Tactile-electronics/WearableTechBadgeWorkshop/images/555flashersmall.gif

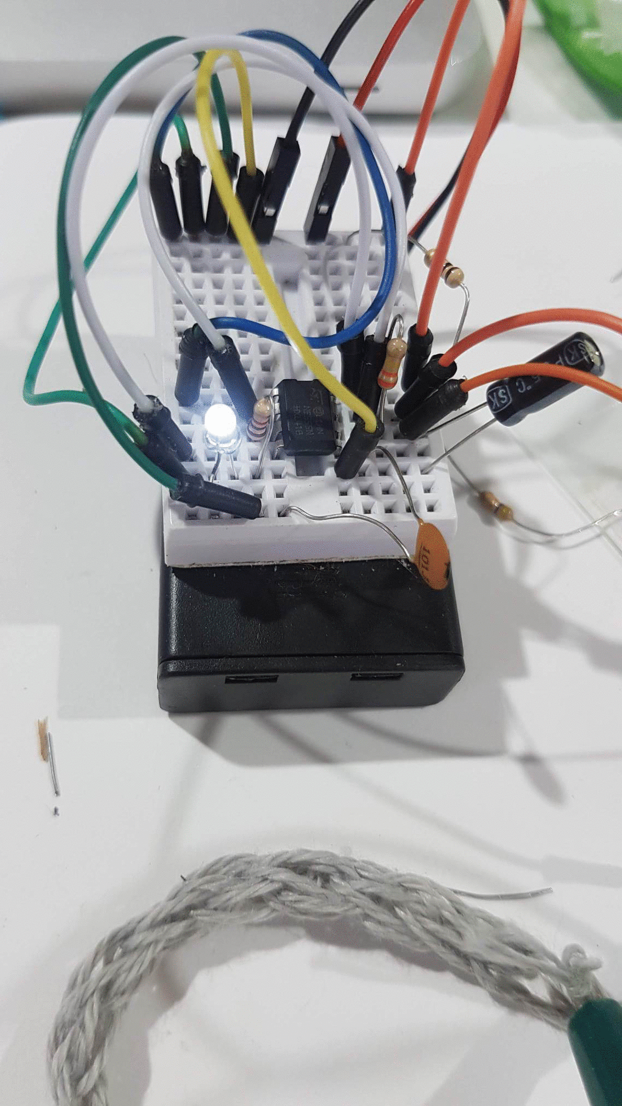
images/555flashersmall.gif
