Tactile-electronics/WearableTechBadgeWorkshop/images/session1/1/basic-sensor-circuit-1.jpg

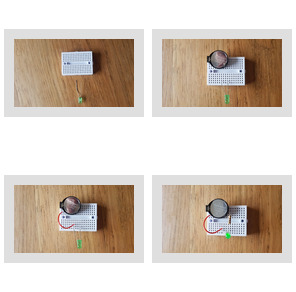
images/session1/1/basic-sensor-circuit-1.jpg
