Tactile-electronics/WearableTechBadgeWorkshop/images/session1/2/6.jpg

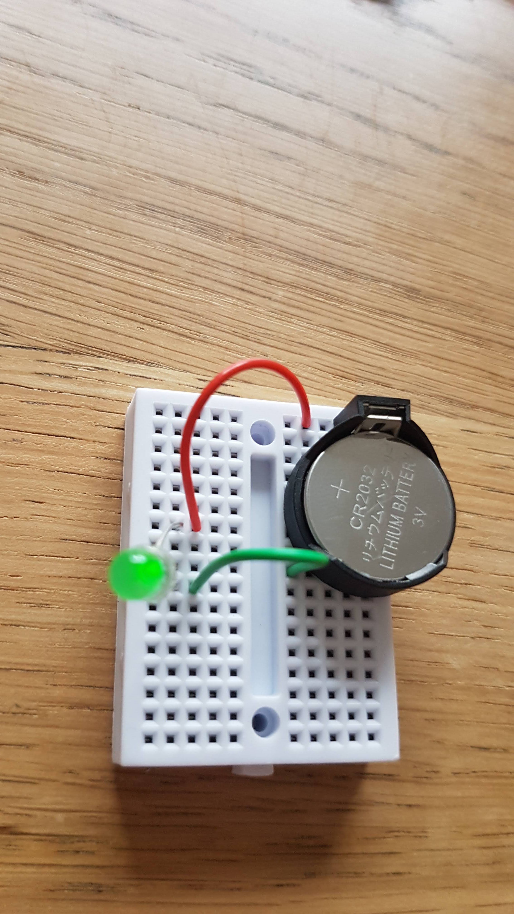
images/session1/2/6.jpg
