Tactile-electronics/WearableTechBadgeWorkshop/images/session1/2/7.jpg

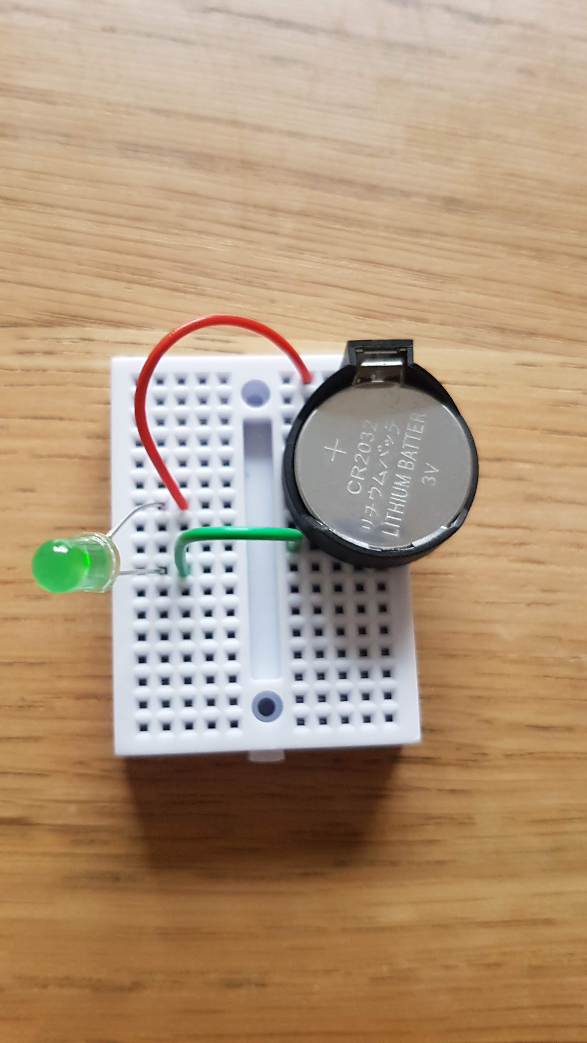
images/session1/2/7.jpg
